scholtzan/led-speakers/model/audio-jack-spacers.stl

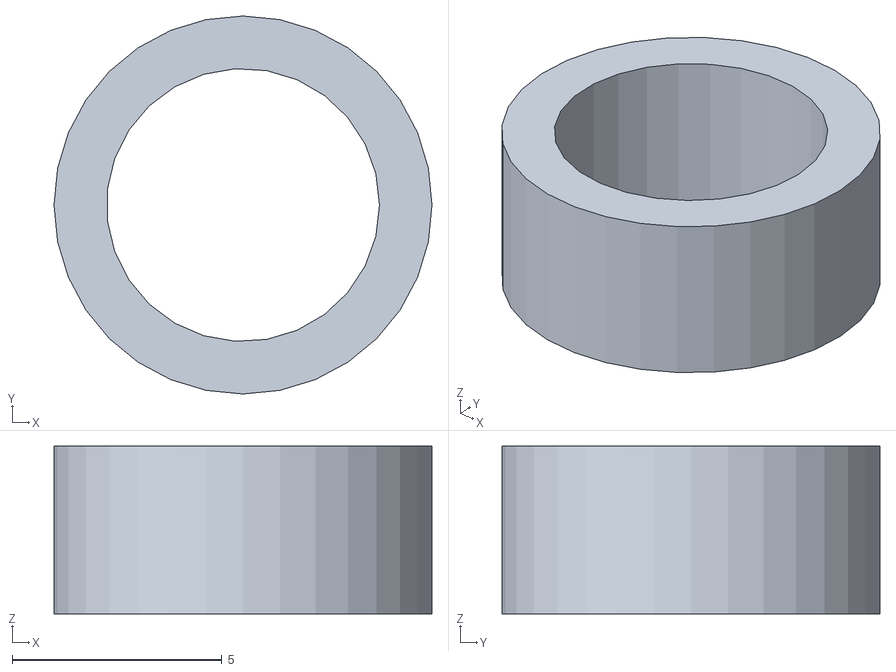
[picture p17: CAD file, 2021-09-24]
model/audio-jack-spacers.stl
9.00 x 9.00 x 4.00
