scholtzan/led-speakers/model/wall-bottom-transparent.stl

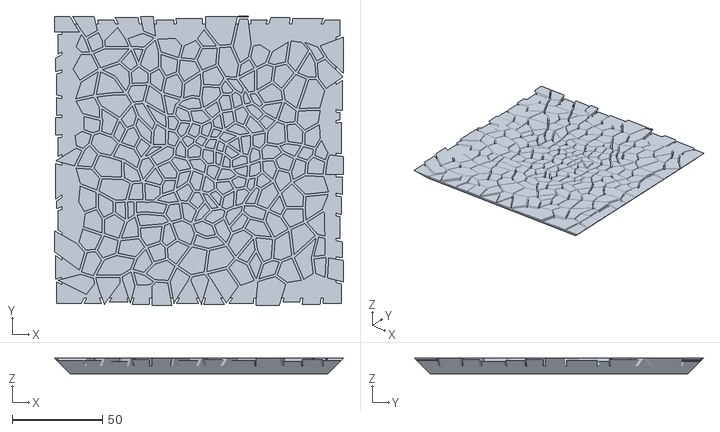
[picture p18: CAD file, 2021-09-24]
model/wall-bottom-transparent.stl
160.0 x 160.0 x 8.60
