scholtzan/led-speakers/src/viz/blend_viz.rs

use chrono::prelude::*;
use chrono::Duration;
use rand::{distributions::Uniform, Rng};
use serde::{Deserialize, Serialize};
use std::collections::HashMap;

use crate::theme::Color;
use crate::viz::PixelViz;
use crate::viz::Viz;

#[derive(Serialize, Deserialize, Debug, PartialEq, Clone)]
/// Visualization Config.
pub struct BlendVizConfig {
    /// Screen friendly name of visualization.
    pub pretty_name: String,

    /// Determines how many neighboring pixels should initially be grouped together when computing offsets.
    pub spread: u8,

    /// Factor determining how fast pixel blend from one color to another.
    pub blend_speed: u8,

    /// Determines the range when computing initial color offsets.
    pub offset_weight: i64,

    /// Factor determining how much the current pixel color changes to the target color in each iteration.
    pub blend_factor: u8,
}

impl BlendVizConfig {
    /// Convert settings in map of strings to visualization config.
    pub fn to_map(&self) -> HashMap<String, String> {
        let mut settings = HashMap::new();
        settings.insert("spread".to_string(), self.spread.to_string());
        settings.insert("blend_speed".to_string(), self.blend_speed.to_string());
        settings.insert("offset_weight".to_string(), self.offset_weight.to_string());
        settings.insert("blend_factor".to_string(), self.blend_factor.to_string());
        settings
    }

    /// Create visualization config from map of strings.
    pub fn from_map(name: String, settings: HashMap<String, String>) -> Self {
        Self {
            pretty_name: name,
            spread: settings
                .get(&"spread".to_string())
                .unwrap_or(&"0".to_string())
                .parse::<u8>()
                .unwrap(),
            blend_speed: settings
                .get(&"blend_speed".to_string())
                .unwrap_or(&"0".to_string())
                .parse::<u8>()
                .unwrap(),
            offset_weight: settings
                .get(&"offset_weight".to_string())
                .unwrap_or(&"0".to_string())
                .parse::<i64>()
                .unwrap(),
            blend_factor: settings
                .get(&"blend_factor".to_string())
                .unwrap_or(&"0".to_string())
                .parse::<u8>()
                .unwrap(),
        }
    }
}

#[derive(Deserialize, Serialize, Clone)]
/// Visualization creating blending pattern.
pub struct BlendViz {
    /// Visualization config.
    pub config: BlendVizConfig,

    /// Total number of pixels.
    total_pixels: usize,

    /// Elapsed time for each pixel until it blends to different color.
    elapsed_time: Vec<DateTime<Utc>>,

    /// Color of each pixel.
    pixels: Vec<PixelViz>,

    /// Colors pixels blend to.
    target_colors: Vec<Color>,
}

#[typetag::serde]
impl Viz for BlendViz {
    fn get_name(&self) -> &str {
        "blend_viz"
    }

    fn get_pretty_name(&self) -> &str {
        &self.config.pretty_name
    }

    fn update(&mut self, input: &Vec<f32>, colors: &Vec<Color>) -> Vec<PixelViz> {
        let total_magnitude: f32 = input.iter().sum();
        let mut rng = rand::thread_rng();

        // magnitude of each frequency band
        let freq_amounts: Vec<i64> = input
            .iter()
            .map(|m| (100.0 * m / (total_magnitude + 0.001)) as i64)
            .collect::<Vec<i64>>();
        let now = Utc::now();

        // update pixel colors
        for pixel_index in 0..self.total_pixels {
            let elapsed = (now - self.elapsed_time[pixel_index]).num_seconds();

            // determine current pixel color based on multipliers
            let current_color = Color {
                r: ((colors[self.pixels[pixel_index].color_index % colors.len()].r as f32)
                    * self.pixels[pixel_index].red_mul) as u8,
                g: ((colors[self.pixels[pixel_index].color_index % colors.len()].g as f32)
                    * self.pixels[pixel_index].green_mul) as u8,
                b: ((colors[self.pixels[pixel_index].color_index % colors.len()].b as f32)
                    * self.pixels[pixel_index].blue_mul) as u8,
            };

            let mut target_color = self.target_colors[pixel_index];

            if elapsed > (self.config.blend_speed as i64) {
                // if time is elapsed, blend to target color
                let mut r = rng.gen_range(0..100) as i64;
                let mut color_index = 0;

                // randomly select next target color
                // frequency bands with larger magnitude are more likely to get selected
                while r > 0 && color_index < freq_amounts.len() - 1 {
                    r -= freq_amounts[color_index as usize];

                    if r > 0 {
                        color_index += 1;
                    }
                }

                // compute target color
                target_color = colors[color_index % colors.len()];
                target_color.r =
                    (target_color.r as f32 * (input[color_index] as f32 / 100.0)) as u8;
                target_color.g =
                    (target_color.g as f32 * (input[color_index] as f32 / 100.0)) as u8;
                target_color.b =
                    (target_color.b as f32 * (input[color_index] as f32 / 100.0)) as u8;
                target_color.r = if target_color.r == 0 {
                    1
                } else {
                    target_color.r
                };
                target_color.g = if target_color.g == 0 {
                    1
                } else {
                    target_color.g
                };
                target_color.b = if target_color.b == 0 {
                    1
                } else {
                    target_color.b
                };

                // update state
                self.target_colors[pixel_index] = target_color;
                self.elapsed_time[pixel_index] = now;
                self.pixels[pixel_index].color_index = color_index;
            }

            // compute blending
            let actual_color = colors[self.pixels[pixel_index].color_index % colors.len()];
            let blend_color = Self::blend(&current_color, &target_color, self.config.blend_factor);

            // update pixels
            self.pixels[pixel_index].red_mul = (blend_color.r as f32) / (actual_color.r as f32);
            self.pixels[pixel_index].green_mul = (blend_color.g as f32) / (actual_color.g as f32);
            self.pixels[pixel_index].blue_mul = (blend_color.b as f32) / (actual_color.b as f32);
        }

        self.pixels.clone()
    }

    fn set_total_pixels(&mut self, pixels: usize) {
        self.total_pixels = pixels;
        self.pixels = vec![PixelViz::default(); pixels];
        self.elapsed_time = vec![Utc::now(); pixels];
        self.target_colors = vec![Color { r: 1, g: 1, b: 1 }; pixels];
        let offsets = self.offsets();

        for pixel_index in 0..self.total_pixels {
            self.elapsed_time[pixel_index] =
                Utc::now() + Duration::milliseconds(offsets[pixel_index]);
        }
    }

    fn get_settings(&self) -> HashMap<String, String> {
        self.config.to_map()
    }

    fn update_settings(&mut self, settings: HashMap<String, String>) {
        let new_settings = BlendVizConfig::from_map(self.get_pretty_name().to_string(), settings);
        self.config = new_settings;
        self.pixels = vec![PixelViz::default(); self.total_pixels];
        self.elapsed_time = vec![Utc::now(); self.total_pixels];
        self.target_colors = vec![Color { r: 1, g: 1, b: 1 }; self.total_pixels];
        let offsets = self.offsets();

        for pixel_index in 0..self.total_pixels {
            self.elapsed_time[pixel_index] =
                Utc::now() + Duration::milliseconds(offsets[pixel_index]);
        }
    }
}

unsafe impl Send for BlendViz {}
unsafe impl Sync for BlendViz {}

impl BlendViz {
    /// Create a new visualization instance.
    pub fn new(config: BlendVizConfig) -> Self {
        BlendViz {
            config,
            total_pixels: 0,
            elapsed_time: Vec::new(),
            pixels: Vec::new(),
            target_colors: Vec::new(),
        }
    }

    /// Compute the initial state of the pixels.
    fn offsets(&mut self) -> Vec<i64> {
        let mut rng = rand::thread_rng();
        let total_pixels = self.total_pixels;

        // random color offsets for each pixel
        let mut offsets: Vec<i64> = (0..total_pixels)
            .map(|_| rng.sample(&Uniform::new(0, self.config.offset_weight)))
            .collect();
        let spread = self.config.spread;

        let mut pixel_index = 0;
        let mut increasing = true;

        // reduce randomization of pixel color offsets
        while pixel_index < total_pixels {
            // ensure that offsets of neighboring pixels are relatively similar
            let mut n = rng.gen_range(0..spread) as usize;
            if pixel_index + n > total_pixels {
                n = total_pixels - pixel_index;
            }

            for i in 0..n {
                if pixel_index + i == 0 {
                    offsets[pixel_index + i] = 0;
                } else {
                    let mut increase = self.config.offset_weight as i64;
                    if !increasing {
                        increase = -(self.config.offset_weight as i64);
                    }

                    offsets[pixel_index + i] = offsets[pixel_index + i - 1] + increase;
                }
            }
            increasing = !increasing;
            pixel_index += n;
        }

        offsets
    }

    /// Blends two colors together and return resulting color.
    fn blend(color_1: &Color, color_2: &Color, blend_factor: u8) -> Color {
        let mut target_color = Color {
            r: color_1.r,
            g: color_1.g,
            b: color_1.b,
        };

        if color_2.r > color_1.r {
            if color_2.r - color_1.r > blend_factor {
                target_color.r += blend_factor;
            }
        } else {
            if color_1.r - color_2.r > blend_factor {
                target_color.r -= blend_factor;
            }
        }

        if color_2.g > color_1.g {
            if color_2.g - color_1.g > blend_factor {
                target_color.g += blend_factor;
            }
        } else {
            if color_1.g - color_2.g > blend_factor {
                target_color.g -= blend_factor;
            }
        }

        if color_2.b > color_1.b {
            if color_2.b - color_1.b > blend_factor {
                target_color.b += blend_factor;
            }
        } else {
            if color_1.b - color_2.b > blend_factor {
                target_color.b -= blend_factor;
            }
        }

        target_color
    }
}
