scholtzan/led-speakers/src/viz/mod.rs

mod blend_viz;
mod center_viz;
mod fading_beat_viz;
mod rotating_viz;
mod solid_beat_viz;
mod solid_viz;
mod sparkle_viz;
mod viz;

pub use blend_viz::BlendViz;
pub use blend_viz::BlendVizConfig;
pub use center_viz::CenterViz;
pub use center_viz::CenterVizConfig;
pub use fading_beat_viz::FadingBeatViz;
pub use fading_beat_viz::FadingBeatVizConfig;
pub use rotating_viz::RotatingViz;
pub use rotating_viz::RotatingVizConfig;
pub use solid_beat_viz::SolidBeatViz;
pub use solid_beat_viz::SolidBeatVizConfig;
pub use solid_viz::SolidViz;
pub use solid_viz::SolidVizConfig;
pub use sparkle_viz::SparkleViz;
pub use sparkle_viz::SparkleVizConfig;
pub use viz::PixelViz;
pub use viz::Viz;
pub use viz::VizRunner;
